vekkuli/chess_clock/chess_clock_fw/max7219.h

/*
 * The MIT License (MIT)
 *
 * Copyright (c) JEMRF
 *
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
 * Module     : max7219.h
 * Author     : Jonathan Evans
 * Description: MAX7219 LED Display Driver
 *
 ********************************************************************************
 * 
 * Modifications by Jaakko Rantala
 * - Modified PIN numbers
 * - Other modifications to support chess clock application
 * 
 ******************************************************************************** 
 */

#ifndef max7219_h
#define max7219_h

#if (ARDUINO >= 100)
#include <Arduino.h>
#else
#include <WProgram.h>
#endif

#include "serial_debug.h"

// MAX7219
#define REG_DECODE 0x09
#define REG_INTENSITY 0x0a
#define REG_SCAN_LIMIT 0x0b
#define REG_SHUTDOWN 0x0c
#define REG_DISPLAY_TEST 0x0f

#define INTENSITY_MIN 0x00
#define INTENSITY_MAX 0x0f

/*
*********************************************************************************************************
* LED Segments:         a
*                     ----
*                   f|    |b
*                    |  g |
*                     ----
*                   e|    |c
*                    |    |
*                     ----  o dp
*                       d
*   Register bits:
*      bit:  7  6  5  4  3  2  1  0
*           dp  a  b  c  d  e  f  g
*********************************************************************************************************
* Example : The letter 'I' is represented by illuminating LED's 'b' and 'c' (refer above diagram)
*           Therfore the binary representation of 'I' is as follows
*
*           abcdefg
*           0110000
*
*           The table below contains all the binary values for the desired font. New font characters
*           can be added or altered as required.
*
*           The DP bit is used to switch on the decimal place LED. DP is not included in the below table
*           but is added in the register within the libary depending on the content being displayed.
*********************************************************************************************************

*/
static const struct
{
    char ascii;
    char segs;
} MAX7219_Font[] = {
    {'A', 0b1110111},
    {'B', 0b1111111},
    {'C', 0b1001110},
    {'D', 0b1111110},
    {'E', 0b1001111},
    {'F', 0b1000111},
    {'G', 0b1011110},
    {'H', 0b0110111},
    {'I', 0b0110000},
    {'J', 0b0111100},
    {'L', 0b0001110},
    {'N', 0b1110110},
    {'O', 0b1111110},
    {'P', 0b1100111},
    {'R', 0b0000101},
    {'S', 0b1011011},
    {'T', 0b0001111},
    {'U', 0b0111110},
    {'Y', 0b0100111},
    {'[', 0b1001110},
    {']', 0b1111000},
    {'_', 0b0001000},
    {'a', 0b1110111},
    {'b', 0b0011111},
    {'c', 0b0001101},
    {'d', 0b0111101},
    {'e', 0b1001111},
    {'f', 0b1000111},
    {'g', 0b1011110},
    {'h', 0b0010111},
    {'i', 0b0010000},
    {'j', 0b0111100},
    {'l', 0b0001110},
    {'n', 0b0010101},
    {'o', 0b1111110},
    {'p', 0b1100111},
    {'r', 0b0000101},
    {'s', 0b1011011},
    {'t', 0b0001111},
    {'u', 0b0011100},
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
};

/// @brief  Specialized display content struct that has fixed 8 positions for characters.
///         Decimal point is not supported. The display consists of two 4-digit
///         7-segment displays. Each display has a colon. The decimal (DP) bit
///         is used to control the colons on each side.
struct Content
{
    char characters[8] = {0, 0, 0, 0, 0, 0, 0, 0};
    bool leftColon = false;
    bool rightColon = false;

    void setSideContent(const char* text, bool left, bool colon = false)
    {
        int offset = left ? 0 : 4;
        memcpy(characters + offset, text, 4);
        if (left)
            leftColon = colon;
        else
            rightColon = colon;
    }

    // Equality operator for comparing display content
    bool operator==(const Content &other) const
    {
        return (memcmp(characters, other.characters, sizeof(characters)) == 0) &&
               (leftColon == other.leftColon) &&
               (rightColon == other.rightColon);
    } 
};

class MAX7219
{
private:
    const int clkPin;
    const int dinPin;
    const int csPin;

public:
    explicit MAX7219(int clkPin, int dinPin, int csPin);
    MAX7219() = delete;
    void Begin();
    void MAX7219_DisplayTestStart();
    void DisplayChar(int digit, char value, bool dp);
    void MAX7219_Write(volatile byte opcode, volatile byte data);
    void MAX7219_ShutdownStop();
    unsigned char MAX7219_LookupCode(char character, unsigned int dp);
    void MAX7219_ShutdownStart();
    void Clear();
    void MAX7219_DisplayTestStop();
    void MAX7219_SetBrightness(char brightness);
    void DisplayText(char *text, int justify);
    void DisplayContent(const Content& content);
};

#endif
