vekkuli/chess_clock/chess_clock_fw/EasyButton.cpp

/**
 * EasyButton.cpp
 * @author Evert Arias
 * @version 2.0.3
 * @license MIT
 */

#include "EasyButton.h"

void EasyButton::begin()
{
	pinMode(_pin, _pu_enabled ? INPUT_PULLUP : INPUT);
	_current_state = _readPin();
	if (_active_low)
	{
		_current_state = !_current_state;
	}
	_time = millis();
	_last_state = _current_state;
	_changed = false;
	_last_change = _time;
}

bool EasyButton::read()
{
	uint32_t read_started_ms = millis();

	bool pinVal = _readPin();

	if (_active_low)
	{
		pinVal = !pinVal;
	}

	if (read_started_ms - _last_change < _db_time)
	{
		// Debounce time has not ellapsed.
		_changed = false;
	}
	else
	{
		// Debounce time ellapsed.
		_last_state = _current_state;				// Save last state.
		_current_state = pinVal;					// Assign new state as current state from pin's value.
		_changed = (_current_state != _last_state); // Report state change if current state vary from last state.
		// If state has changed since last read.
		if (_changed)
		{
			// State changed.
			// Save current millis as last change time.
			_last_change = read_started_ms;
		}
	}

	if (wasReleased())
	{
		if (!_was_btn_held)
		{
			if (_pressed_callback)
			{
				_pressed_callback();
			}
		}
		// Button was not held.
		else
		{
			_was_btn_held = false;
		}

		// Since button released, reset _pressed_for_callbackCalled value.
		_held_callback_called = false;
	}
	else if (isPressed() && _read_type == EASYBUTTON_READ_TYPE_POLL)
	{
		_checkPressedTime();
	}

	_time = read_started_ms;

	return _current_state;
}

bool EasyButton::_readPin()
{
	return digitalRead(_pin);
}

bool EasyButton::supportsInterrupt()
{
	return (digitalPinToInterrupt(_pin) != NOT_AN_INTERRUPT);
}

void EasyButton::enableInterrupt(EasyButton::callback_t callback)
{
	attachInterrupt(digitalPinToInterrupt(_pin), callback, CHANGE);
	_read_type = EASYBUTTON_READ_TYPE_INTERRUPT;
}

void EasyButton::disableInterrupt()
{
	detachInterrupt(digitalPinToInterrupt(_pin));
	_read_type = EASYBUTTON_READ_TYPE_POLL;
}

void EasyButton::update()
{
	if (!_was_btn_held)
	{
		_checkPressedTime();
	}
}
