vekkuli/chess_clock/chess_clock_fw/EasyButtonBase.h

/**
 * EasyButtonBase.h
 * @author Evert Arias
 * @version 2.0.3
 * @license MIT
 */

#ifndef _EasyButtonBase_h
#define _EasyButtonBase_h

#include <Arduino.h>

class EasyButtonBase
{
public:
    typedef void (*callback_t)();
    EasyButtonBase(bool active_low) : _active_low(active_low) {}
    virtual void begin() = 0;                                                   // Initialize a button object and the pin it's connected to.
    virtual bool read() = 0;                                                    // Returns the current debounced button state, true for pressed, false for released.
    void onPressed(callback_t callback);                                        // Call a callback function when the button has been pressed and released.
    void onPressedFor(uint32_t duration, callback_t callback);                  // Call a callback function when the button has been held for at least the given number of milliseconds.

    bool isPressed();                    // Returns true if the button state was pressed at the last read.
    bool isReleased();                   // Returns true if the button state was released at the last read.
    bool wasPressed();                   // Returns true if the button state at the last read was pressed.
    bool wasReleased();                  // Returns true if the button state at the last read was released.
    bool pressedFor(uint32_t duration);  // Returns true if the button state at the last read was pressed, and has been in that state for at least the given number of milliseconds.
    bool releasedFor(uint32_t duration); // Returns true if the button state at the last read was released, and has been in that state for at least the given number of milliseconds.

    uint32_t _held_threshold; // Held threshold.

    callback_t _pressed_callback = nullptr;     // Callback function for pressed events.
    callback_t _pressed_for_callback = nullptr; // Callback function for pressedFor events.
    bool _held_callback_called;       // Indicate if button long press has been notified.
    bool _active_low;                 // Inverts button logic. If true, low = pressed else high = pressed.
    bool _current_state;              // Current button state, true = pressed.
    bool _last_state;                 // Previous button state, true = pressed.
    bool _changed;                    // Has the state change since last read.
    uint32_t _time;                   // Time of current state.
    uint32_t _last_change;            // Time of last state change.
    bool _was_btn_held;               // Indicate if button was held.

    void _checkPressedTime(); // Verify if pressed_for_callback should be called.
};

#endif
